boningdong/Smart-Lamp/Firmware/Modules/GeneralFunctions.h

/*
 * GeneralFunctions.h
 *
 *  Created on: 2016Äê5ÔÂ17ÈÕ
 *      Author: DBN
 */

#ifndef MODULES_GENERALFUNCTIONS_H_
#define MODULES_GENERALFUNCTIONS_H_

void delay(unsigned int);



#endif /* MODULES_GENERALFUNCTIONS_H_ */
