boningdong/Smart-Lamp/Firmware/Modules/I2C.h

/*
 * I2C.h
 *
 *  Created on: 2016Äê4ÔÂ30ÈÕ
 *      Author: DBN
 */

#ifndef MODULES_I2C_H_
#define MODULES_I2C_H_

void I2C_init();
void SendData(unsigned char, unsigned char);

#endif /* MODULES_I2C_H_ */
