boningdong/Smart-Lamp/Firmware/Modules/SysClock.h

/*
 * SysClock.h
 *
 *  Created on: 2016Äê4ÔÂ30ÈÕ
 *      Author: DBN
 */

#ifndef MODULES_SYSCLOCK_H_
#define MODULES_SYSCLOCK_H_

void Clock_init();
void SMCLK_Detectable();

#endif /* MODULES_SYSCLOCK_H_ */
