boningdong/Smart-Lamp/Firmware/Modules/Timer.h

/*
 * Timer.h
 *
 *  Created on: 2016Äê5ÔÂ18ÈÕ
 *      Author: DBN
 */

#ifndef MODULES_TIMER_H_
#define MODULES_TIMER_H_

void Timer_Init();
void Stop_Timer();
void Start_Timer();


#endif /* MODULES_TIMER_H_ */
