boningdong/Smart-Lamp/Firmware/Modules/TouchPad.h

/*
 * IO.h
 *
 *  Created on: 2016Äê5ÔÂ17ÈÕ
 *      Author: DBN
 */

#ifndef MODULES_TOUCHPAD_H_
#define MODULES_TOUCHPAD_H_

enum {
    down = 0,
    up = 1
} dim_dir = down;

void TouchPad_Init();



#endif /* MODULES_TOUCHPAD_H_ */
